jamestansx/qms/docs/pictures/add_appointment_name.jpeg

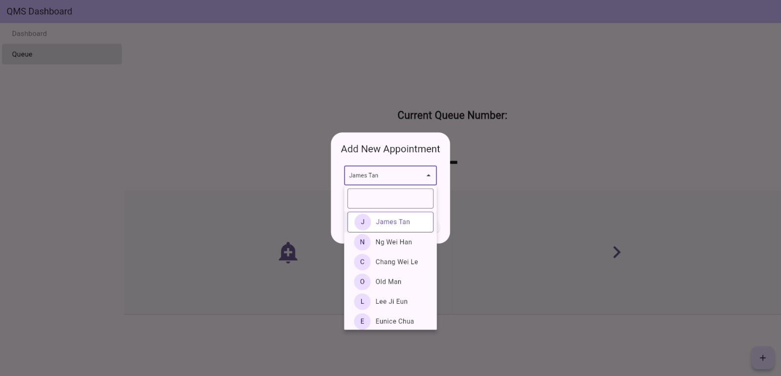
docs/pictures/add_appointment_name.jpeg
