jamestansx/qms/docs/pictures/dashboard_add_device_name.jpeg

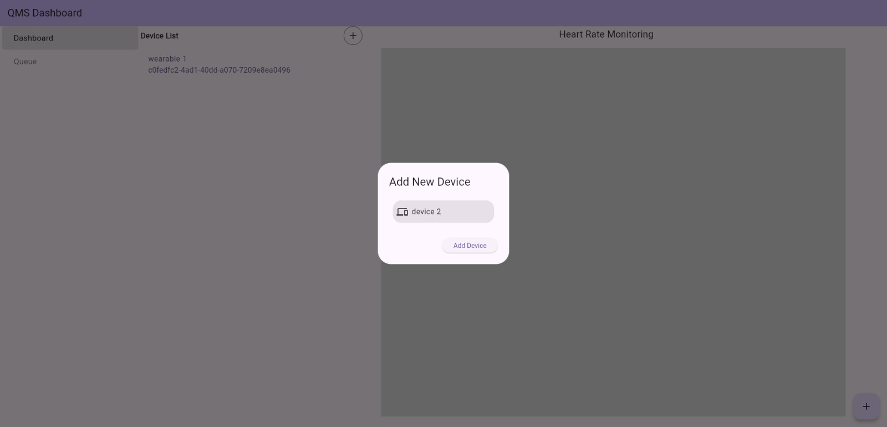
docs/pictures/dashboard_add_device_name.jpeg
