jamestansx/qms/docs/pictures/dashboard_device_list.jpeg

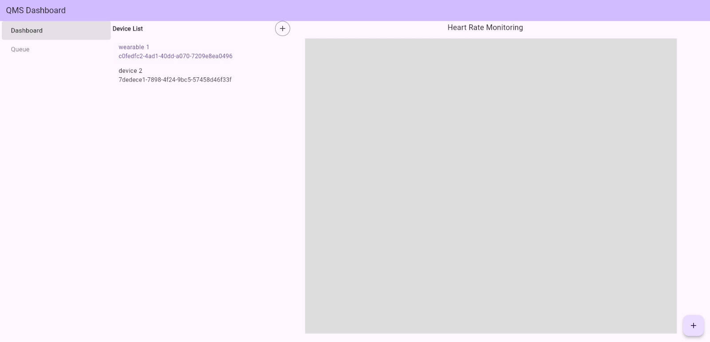
docs/pictures/dashboard_device_list.jpeg
