jamestansx/qms/docs/pictures/dashboard_fall_alert.jpeg

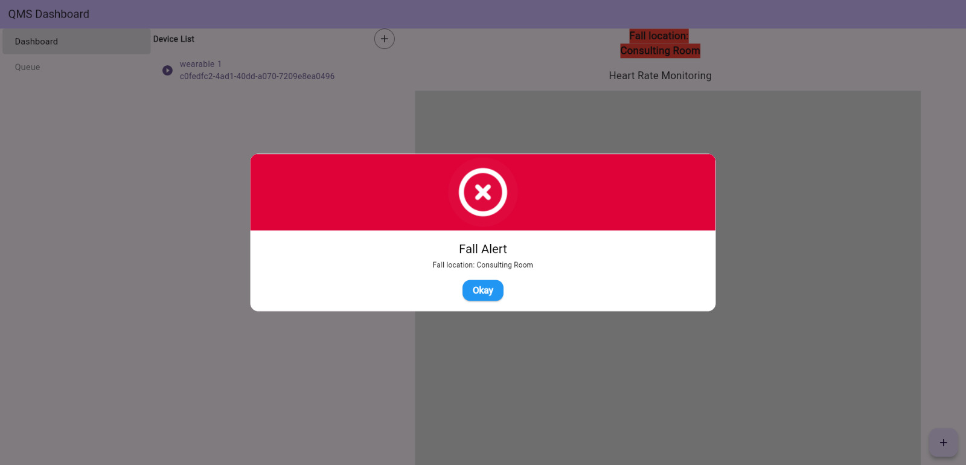
docs/pictures/dashboard_fall_alert.jpeg
