jamestansx/qms/docs/pictures/dashboard_heart_rate_monitor(2).jpeg

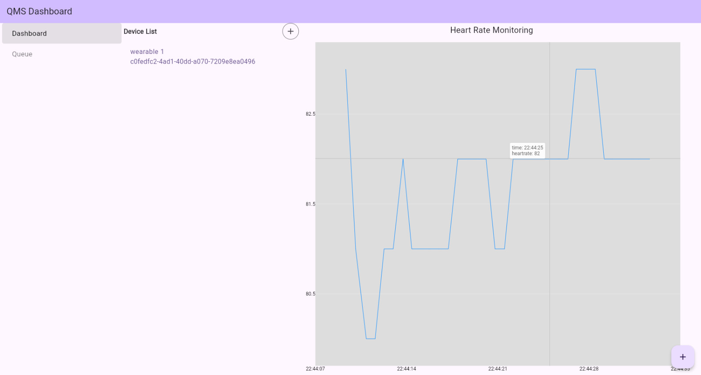
docs/pictures/dashboard_heart_rate_monitor(2).jpeg
