jamestansx/qms/docs/pictures/dashboard_queue_status.jpeg

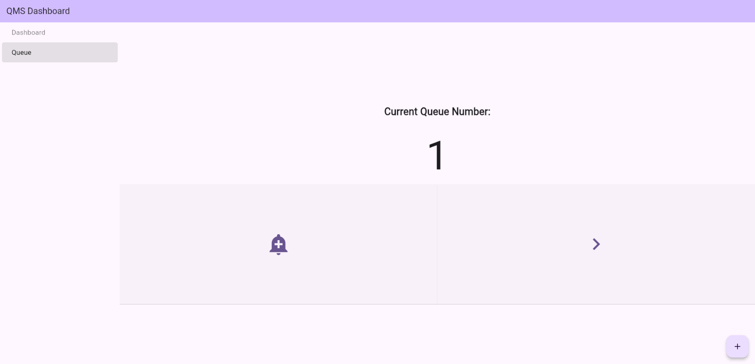
docs/pictures/dashboard_queue_status.jpeg
