jamestansx/qms/docs/pictures/flutter_appointment_list.jpeg

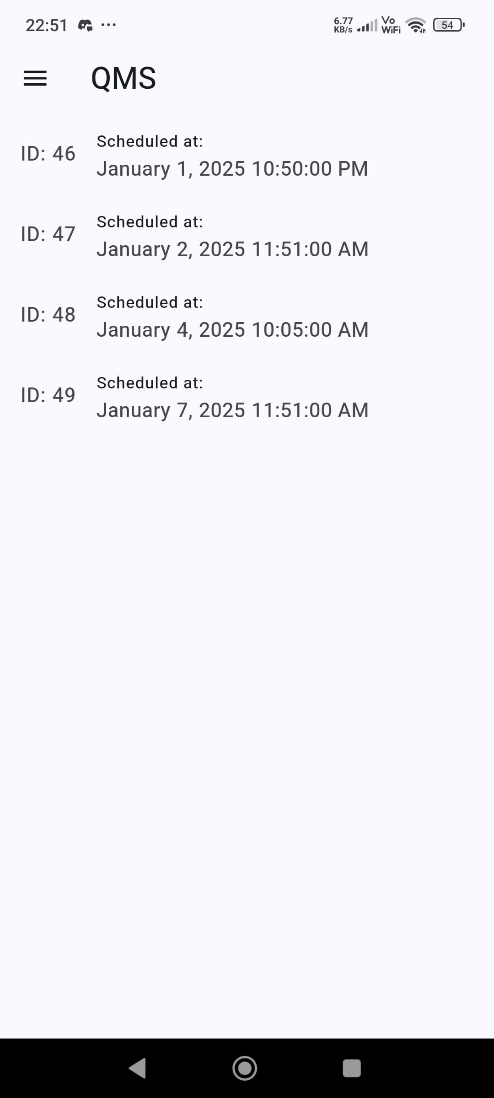
docs/pictures/flutter_appointment_list.jpeg
