jamestansx/qms/docs/pictures/flutter_qr.jpeg

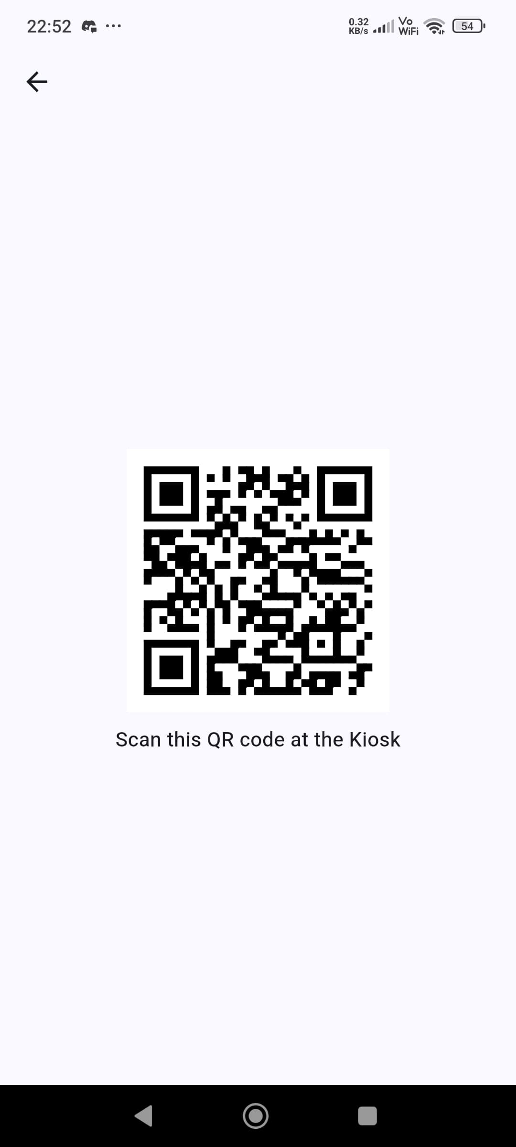
docs/pictures/flutter_qr.jpeg
