jamestansx/qms/docs/pictures/flutter_queue_number.jpeg

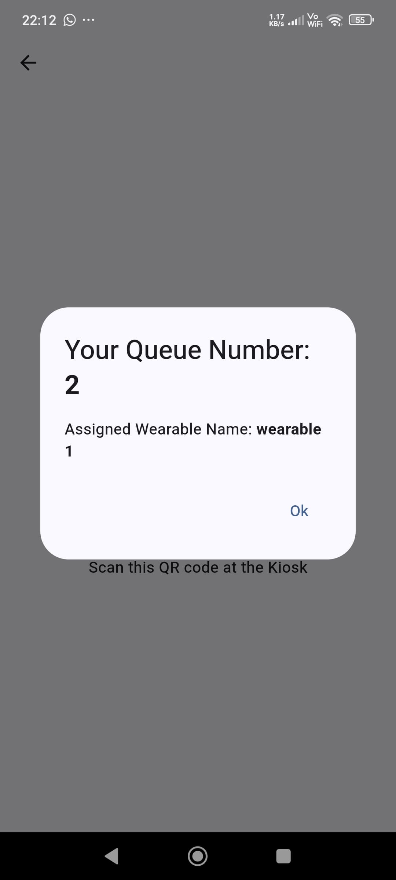
docs/pictures/flutter_queue_number.jpeg
