jamestansx/qms/docs/pictures/flutter_queue_number_no_device.jpeg

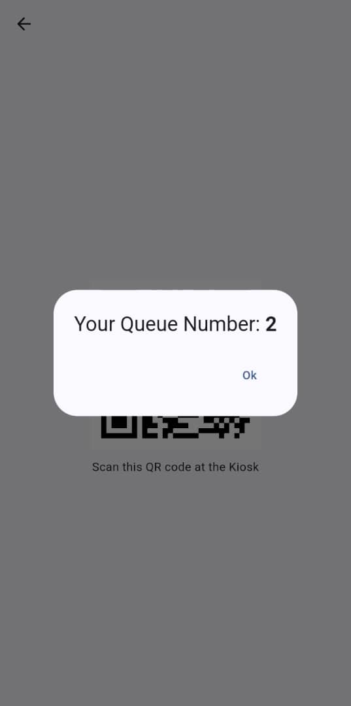
docs/pictures/flutter_queue_number_no_device.jpeg
