jamestansx/qms/docs/pictures/flutter_queue_status.jpeg

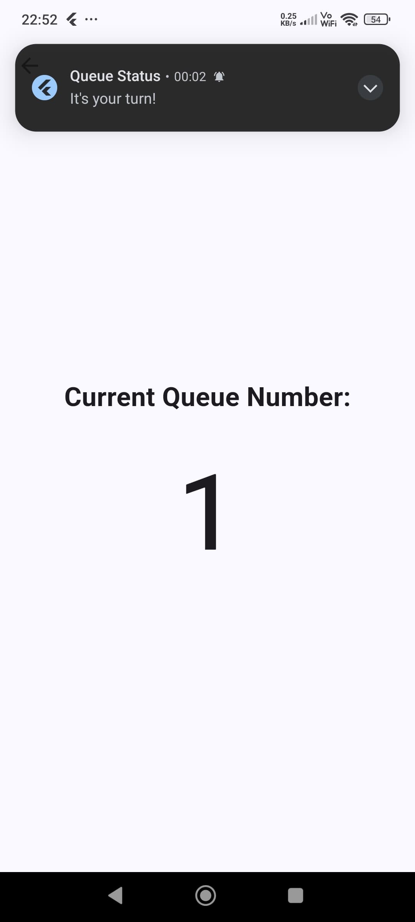
docs/pictures/flutter_queue_status.jpeg
