jamestansx/qms/docs/pictures/flutter_signup_page.jpeg

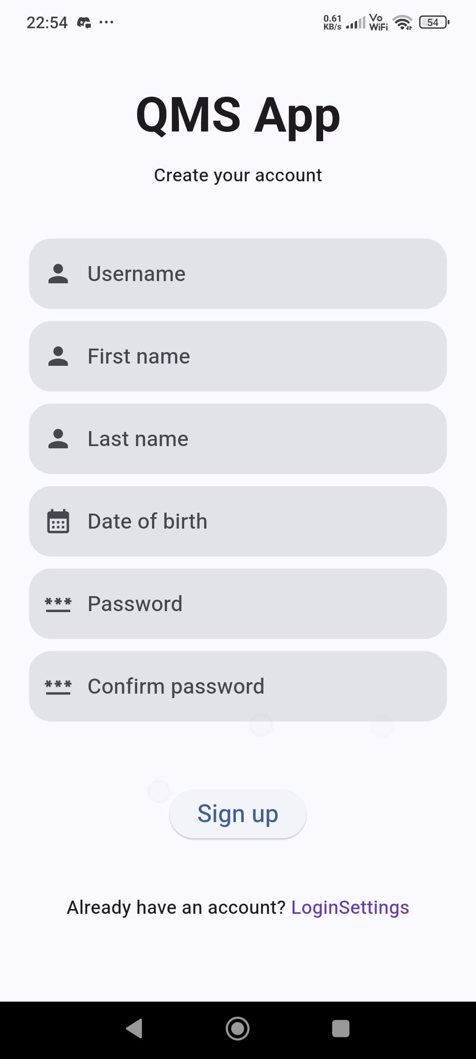
docs/pictures/flutter_signup_page.jpeg
