jamestansx/qms/docs/pictures/sse_fall_detect.jpeg

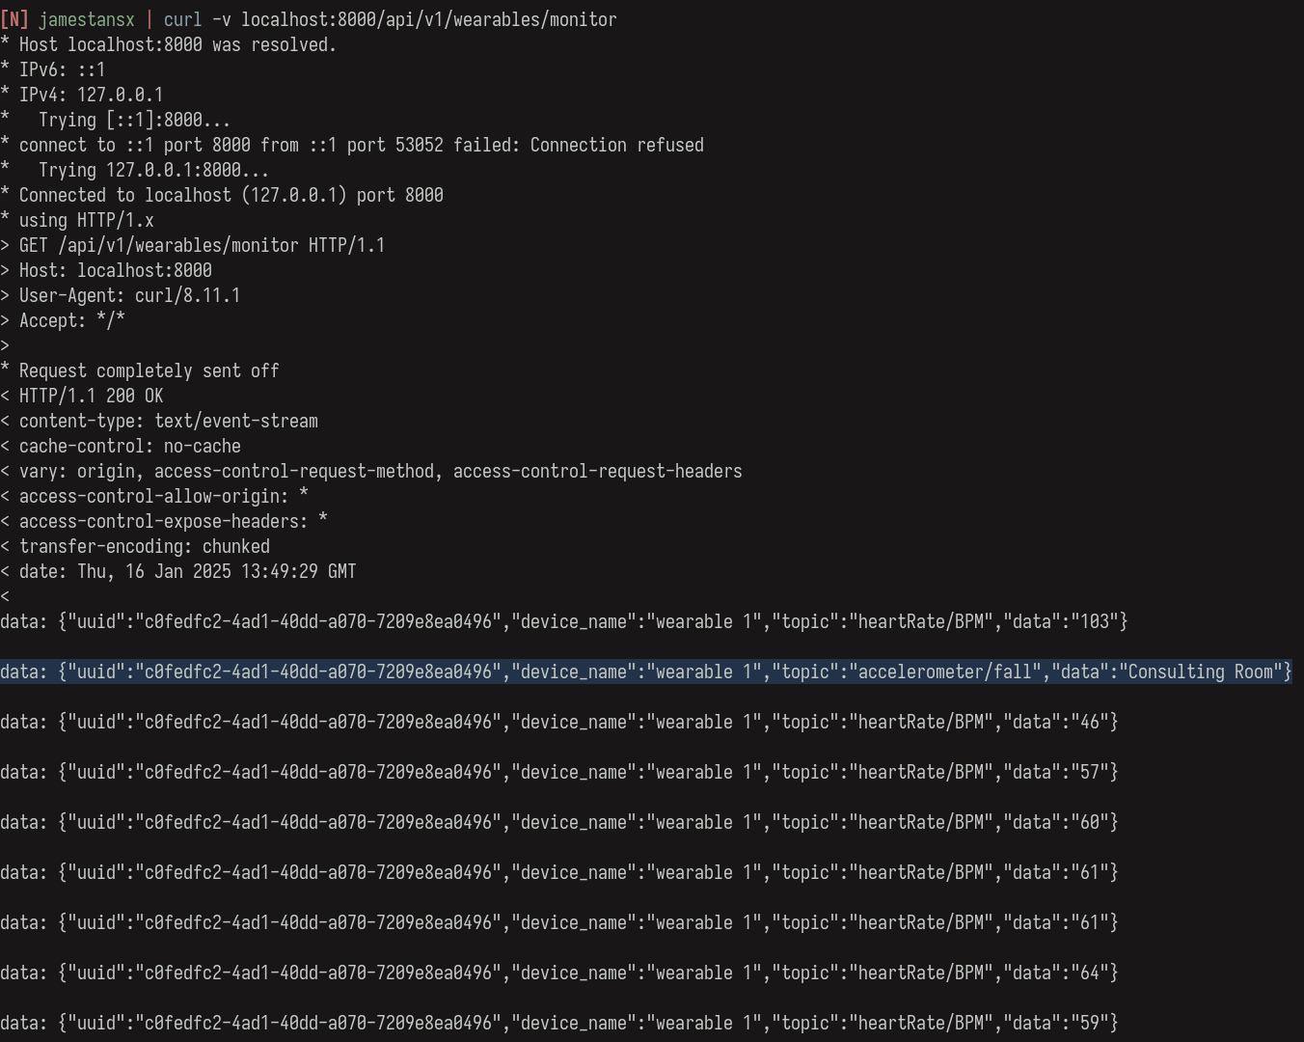
docs/pictures/sse_fall_detect.jpeg
